S0urceror/MSX-USB/test/usb_via_arduino/src/main.parallel.cpp

// USB-HID - application that discovers attached USB devices to CH376s
// Copyright 2019 - Sourceror (Mario Smit)

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
#include <stdio.h>
#include <fcntl.h>
#include <termios.h>
#include <strings.h>
#include <string.h>
#include <unistd.h>
#include <stdlib.h>
#include <vector>
#include <string>
#include <locale>
#include <codecvt>
#include <thread>
#include <chrono>
#include <ctime>
#include <iostream>
#include <stdio.h>
#include <iomanip>

#define BOOT_PROTOCOL 0
#define HID_CLASS 0x03
#define HID_BOOT 0x01
#define HID_KEYBOARD 0x01
#define HID_MOUSE 0x02

//#define   B115200 0010002
//#define   B230400 0010003
#define   B460800 0010004
#define   B500000 0010005
#define   B576000 0010006
#define   B921600 0010007
#define  B1000000 0010010
#define  B1152000 0010011
#define  B1500000 0010012
#define  B2000000 0010013
#define  B2500000 0010014
#define  B3000000 0010015
#define  B3500000 0010016
#define  B4000000 0010017
#define BAUDRATE B115200
int serial=-1;

#define CH376_CMD_GET_IC_VER 0x01
#define CH375_CMD_SET_USB_SPEED 0x04
#define CH375_CMD_RESET_ALL 0x05
#define CH375_CMD_CHECK_EXIST 0x06
#define CH375_CMD_SET_USB_MODE 0x15
#define CH375_CMD_TEST_CONNECT 0x16
#define CH375_CMD_GET_STATUS 0x22
#define CH375_CMD_SET_USB_ADDR 0x13
#define CH375_CMD_SET_ENDP6 0x1C
#define CH375_CMD_SET_ENDP7 0x1D
#define CH375_CMD_RD_USB_DATA 0x27
#define CH375_CMD_RD_USB_DATA_UNLOCK     0x28
//#define CH375_CMD_WR_USB_DATA7 0x2B
#define CH375_CMD_WR_HOST_DATA 0x2C
#define CH376_CMD_SET_FILE_NAME 0x2F
#define CH376_CMD_DISK_CONNECT 0x30
#define CH376_CMD_DISK_MOUNT 0x31
#define CH376_CMD_OPEN_FILE 0x32
#define CH376_CMD_FILE_ENUM_GO 0x33
#define CH376_CMD_FILE_CLOSE 0x36
#define CH376_CMD_DIR_INFO_READ 0x37

#define CH376_CMD_BYTE_READ 0x3a
#define CH376_CMD_BYTE_RD_GO 0x3b
#define CH375_USB_INT_DISK_READ 0x1d

#define CH376_CMD_CLR_STALL 0x41
#define CH375_CMD_SET_ADDRESS 0x45
#define CH375_CMD_GET_DESCR 0x46
#define CH375_CMD_SET_CONFIG 0x49
#define CH375_CMD_ISSUE_TOKEN 0x4F
#define CH375_CMD_ISSUE_TKN_X 0x4E
#define CH375_CMD_ABORT_NAK 0x17
#define CH376_CMD_GET_REGISTER 0x0A
#define CH376_CMD_SET_REGISTER 0x0B

#define CH375_USB_MODE_HOST_NON_SOF 0x05
#define CH375_USB_MODE_HOST 0x06
#define CH375_USB_MODE_HOST_RESET 0x07

#define CH375_USB_ERR_OPEN_DIR 0x41
#define CH375_USB_ERR_MISS_FILE 0x42
#define CH375_USB_ERR_FOUND_NAME 0x43

#define CH375_USB_INT_SUCCESS 0x14
#define CH375_USB_INT_CONNECT 0x15
#define CH375_USB_INT_DISCONNECT 0x16
#define CH375_USB_INT_BUF_OVER 0x17
#define CH375_USB_INT_USB_READY 0x18

#define CH375_CMD_RET_SUCCESS 0x51
#define CH375_CMD_RET_ABORT 0x52

#define CH375_USB_DEVICE_DESCRIPTOR 0x01
#define CH375_USB_CONFIGURATION_DESCRIPTOR 0x02
#define CH375_USB_INTERFACE_DESCRIPTOR 0x04
#define CH375_USB_ENDPOINT_DESCRIPTOR 0x05

//--- PIDs
#define CH_PID_SETUP 0x0D
#define CH_PID_IN  0x09
#define CH_PID_OUT 0x01

uint8_t device_counter=1;
uint8_t max_packet_size;
#ifdef _VERBOSE_DEBUG
std::chrono::system_clock::time_point curtime;
#endif

typedef struct __attribute__((packed)) _USB_DEVICE_DESCRIPTOR {
     uint8_t bLength;
     uint8_t bDescriptorType;
     uint16_t bcdUSB;
     uint8_t bDeviceClass;
     uint8_t bDeviceSubClass;
     uint8_t bDeviceProtocol;
     uint8_t bMaxPacketSize0;
     uint16_t idVendor;
     uint16_t idProduct;
     uint16_t bcdDevice;
     uint8_t iManufacturer;
     uint8_t iProduct;
     uint8_t iSerial;
     uint8_t bNumConfigurations;
} USB_DEVICE_DESCRIPTOR;
USB_DEVICE_DESCRIPTOR device;

 typedef struct __attribute__((packed)) _USB_CONFIG_DESCRIPTOR {
     uint8_t bLength;
     uint8_t bDescriptorType;
     uint16_t wTotalLength;
     uint8_t bNumInterfaces;
     uint8_t bConfigurationvalue;
     uint8_t iConfiguration;
     uint8_t bmAttributes;
     uint8_t bMaxPower;
 } USB_CONFIG_DESCRIPTOR;

typedef struct __attribute__((packed)) _USB_HID_DESCRIPTOR {
    uint8_t bLength;
    uint8_t bDescriptorType;
    uint16_t hid_version;
    uint8_t country_code;
    uint8_t num_descriptors;
    uint8_t descriptor_type;
    uint16_t descriptor_length;
} USB_HID_DESCRIPTOR;

 typedef struct __attribute__((packed)) _USB_INTERF_DESCRIPTOR {
     uint8_t bLength;
     uint8_t bDescriptorType;
     uint8_t bInterfaceNumber;
     uint8_t bAlternateSetting;
     uint8_t bNumEndpoints;
     uint8_t bInterfaceClass;
     uint8_t bInterfaceSubClass;
     uint8_t bInterfaceProtocol;
     uint8_t iInterface;
 } USB_INTERF_DESCRIPTOR;

 typedef struct __attribute__((packed)) _USB_ENDPOINT_DESCRIPTOR {
     uint8_t bLength;
     uint8_t bDescriptorType;
     uint8_t bEndpointAddress;
     uint8_t bmAttributes;
     uint16_t wMaxPacketSize;
     uint8_t bInterval;
 } USB_ENDPOINT_DESCRIPTOR;

typedef struct __attribute__((packed)) _USB_ETHERNET_DESCRIPTOR {
     uint8_t bLength;
     uint8_t bDescriptorType;
     uint8_t bDescriptorSubType;
     uint8_t iMACAddress;
     uint32_t bmEthernetStatistics;
     uint16_t wMaxSegmentSize;
     uint16_t wNumberMCFilters;
     uint8_t bNumberPowerFilters;
 } USB_ETHERNET_DESCRIPTOR;

typedef struct __attribute__((packed)) _USB_ETHERNET_HEADER_DESCRIPTOR {
     uint8_t bLength;
     uint8_t bDescriptorType;
     uint8_t bDescriptorSubType;
     uint16_t bcdCDC;
 } USB_ETHERNET_HEADER_DESCRIPTOR;

typedef struct __attribute__((packed)) _USB_ETHERNET_UNION_DESCRIPTOR {
     uint8_t bLength;
     uint8_t bDescriptorType;
     uint8_t bDescriptorSubType;
     uint8_t bControlInterface;
     uint8_t bSubordinateInterface0;
     uint8_t bSubordinateInterface1;
     uint8_t bSubordinateInterface2;
     uint8_t bSubordinateInterface3;
 } USB_ETHERNET_UNION_DESCRIPTOR;

typedef struct __attribute__((packed)) _USB_HUB_DESCRIPTOR 
{
     uint8_t bLength;
     uint8_t bDescriptorType;
     uint8_t bNrPorts;
     uint16_t wHubCharacteristics;
     uint8_t bPwrOn2PwrGood;
     uint8_t bHubContrCurrent;
     uint8_t DeviceRemovable;
     uint8_t PortPwrCtrlMask;
} USB_HUB_DESCRIPTOR;

struct _hid_info 
{
    uint8_t mouse_endpoint,mouse_millis,mouse_interface=255;
    uint16_t mouse_packetsize;
    uint8_t keyboard_endpoint,keyboard_millis,keyboard_interface=255;
    uint16_t keyboard_packetsize;
    uint8_t configuration_id=0;
    uint8_t device_address;
}* hid_info=NULL;
struct _ethernet_info 
{
    uint8_t ethernet_data_interface=255,ethernet_control_interface=255;
    uint8_t ethernet_interrupt_endpoint,ethernet_bulk_in_endpoint,ethernet_bulk_out_endpoint;
    uint8_t ethernet_interrupt_millis;
    uint16_t ethernet_interrupt_packetsize,ethernet_bulk_in_packetsize,ethernet_bulk_out_packetsize;
    uint8_t configuration_id=0;
    uint8_t ethernet_alternate_setting;
    uint8_t device_address;
}* ethernet_info=NULL;
struct _hub_info
{
    uint8_t hub_interface=255;
    uint8_t configuration_id=0;
    uint8_t hub_interrupt_endpoint;
    uint16_t hub_interrupt_packetsize;
    uint8_t hub_interrupt_millis;
    uint8_t device_address;
}* hub_info=NULL;
struct _storage_info
{
    uint8_t interface_id=255;
    uint8_t configuration_id=0;
    uint8_t bulk_in_endpoint_id=0;
    uint8_t bulk_in_packetsize;
    uint8_t bulk_in_toggle=0;
    uint8_t bulk_out_endpoint_id=0;
    uint8_t bulk_out_packetsize;
    uint8_t bulk_out_toggle=0;
    uint8_t device_address;
    uint32_t tag = 1;
}* storage_info=NULL;
typedef struct __attribute__((packed)) _command_block_wrapper 
{
    uint32_t dCBWSignature = 0x43425355;
    uint32_t dCBWTag = 1;
    uint32_t dCBWDataTransferLength;
    uint8_t bmCBWFlags;
    uint8_t bCBWLUN;
    uint8_t bCBWCBLength;
    uint8_t data [16];
} command_block_wrapper;
typedef struct __attribute__((packed)) _command_status_wrapper 
{
    uint32_t dCBWSignature;
    uint32_t dCBWTag;
    uint32_t dCSWDataResidue;
    uint8_t bCSWStatus;
} command_status_wrapper;
typedef struct __attribute__((packed)) _scsi_inquiry
{
    uint8_t bOperationCode = 0x12;
    uint8_t bLUN=0;
    uint8_t bReserved1=0;
    uint8_t bReserved2=0;
    uint8_t bAllocationLength = 0x24;
    uint8_t bReserved3=0;
    //uint8_t pad [6] = {0,0,0,0,0,0};
} scsi_inquiry;
typedef struct __attribute__((packed)) _scsi_read10
{
    uint8_t bOperationCode = 0x28;
    uint8_t bLUN=0;
    uint32_t dLBA=0;
    uint8_t bReserved1=0;
    uint16_t wTransferLength=0;
    uint8_t bReserved2=0;
    //uint8_t pad [2]={0,0};
} scsi_read10;
typedef struct __attribute__((packed)) _scsi_request_sense
{
    uint8_t bOperationCode = 0x03;
    uint8_t bLUN=0;
    uint8_t bReserved1=0;
    uint8_t bReserved2=0;
    uint8_t bAllocationLength = 18;
    uint8_t bReserved3=0;
    //uint8_t pad [6] = {0,0,0,0,0,0};
} scsi_request_sense;
typedef struct __attribute__((packed)) _scsi_test_unit_ready
{
    uint8_t bOperationCode = 0x00;
    uint8_t bLUN=0;
    uint8_t bReserved1=0;
    uint8_t bReserved2=0;
    uint8_t bReserved3=0;
    uint8_t bReserved4=0;
    //uint8_t pad [6] = {0,0,0,0,0,0};
} scsi_test_unit_ready;
typedef struct __attribute__((packed)) _scsi_mode_sense6
{
    uint8_t bOperationCode = 0x1a;
    uint8_t bLUN=0;
    uint8_t bPageCode=0;
    uint8_t bSubpageCode=0;
    uint8_t bAllocationLength=0;
} scsi_mode_sense6;
typedef struct __attribute__((packed)) _scsi_capacity
{
    uint8_t bOperationCode = 0x25;
    uint8_t bLUN=0;
    uint8_t pad[8] = {0,0,0,0,0,0,0,0};
} scsi_capacity;

bool VERBOSE=1;
void print_buffer (uint8_t* data, uint16_t length)
{
    if (VERBOSE==0)
        return;

    for (int i=0;i<length;i++)
    {
        if ((i%16)==0)
            printf ("\n");
        if ((i%4)==0)
            printf (" ");
        printf ("%02x ",*(data+i));
    }
    printf ("\n");
}

void error (char const * msg)
{
    printf ("ERROR: %s\n",msg);
    exit(0);
}

void init_serial (const char* device)
{
    serial = open(device, O_RDWR | O_NOCTTY | O_NONBLOCK);
    if(serial == -1)
      error( "failed to open port" );
    if(!isatty(serial))
      error( "not serial" );
    fcntl(serial, F_SETFL, 0);
    
    struct termios  config;
    bzero(&config, sizeof(config));
    config.c_cflag |= CS8 | CLOCAL | CREAD;
    config.c_iflag |= IGNPAR;
    cfsetispeed (&config, B230400);
    cfsetospeed (&config, B230400);
     
    config.c_cc[VTIME]    = 1;   /* wait 0.1 * VTIME on new characters to arrive when blocking */
    config.c_cc[VMIN]     = 1;   /* blocking read until 1 chars received */
    
    tcflush(serial, TCIFLUSH);
    tcsetattr(serial, TCSANOW, &config); 
}

// LOW_LEVEL serial communication to CH376
///////////////////////////////////////////////////////////////////////////
const uint8_t WR_COMMAND = 1;
const uint8_t RD_STATUS = 2;
const uint8_t WR_DATA = 3;
const uint8_t RD_DATA = 4;
const uint8_t RD_INT = 5;
const uint8_t RD_DATA_MULTIPLE = 6;
const uint8_t WR_DATA_MULTIPLE = 7;
const uint8_t DATA_DUMP = 10;
const uint8_t SPI_WRITE_MULTIPLE = 11;

void testspeed ()
{
    uint8_t new_value;
    uint8_t cmd = DATA_DUMP;
    int i;
    write (serial, &cmd, 1);

    auto t1 = std::chrono::high_resolution_clock::now();
    for (i=0;i<10*512;i++) {
        int bytes = read (serial,&new_value,1);
        if (bytes!=1)
            error ("Serial max speed test did not receive all expected bytes");
        if (new_value!=0xaa)
            error ("Wrong data returned");
    }
    auto t2 = std::chrono::high_resolution_clock::now();
    auto duration = std::chrono::duration_cast<std::chrono::microseconds>( t2 - t1 ).count();
    std::cout << "Serial max read speed: " << i / (duration/1000000.0) << " bytes/second" << std::endl;
}
#ifdef _VERBOSE_DEBUG
std::string getCommandName(uint8_t command)
{
  std::string cmdstr;
  switch (command)
  {
    case 0x01:  cmdstr = "CH_CMD_GET_IC_VER";
                break;
    case 0x04:  cmdstr = "CH_CMD_SET_SPEED";
                break;
    case 0x05:  cmdstr = "CH_CMD_RESET_ALL";
                break;
    case 0x06:  cmdstr = "CH_CMD_CHECK_EXIST";
                break;
    case 0x0b:  cmdstr = "CH_CMD_SET_REGISTER"; // SET_RETRY, SD0_INT
                break;
    case 0x0f:  cmdstr = "CH_CMD_DELAY_100US";
                break;
    case 0x13:  cmdstr = "CH_CMD_SET_USB_ADDR";
                break;
    case 0x15:  cmdstr = "CH_CMD_SET_USB_MODE";
                break;
    case 0x16:  cmdstr = "CH_CMD_TEST_CONNECT";
                break;
    //case 0x17:  cmdstr = "CH_CMD_ABORT_NAK";
    //            break;
    case 0x22:  cmdstr = "CH_CMD_GET_STATUS";
                break;
    case 0x27:  cmdstr = "CH_CMD_RD_USB_DATA0";
                break;
    case 0x2c:  cmdstr = "CH_CMD_WR_HOST_DATA";
                break;
    case 0x4e:  cmdstr = "CH_CMD_ISSUE_TKN_X";
                break;
    case 0x46:  cmdstr = "CH_CMD_GET_DESCR";
                break;
    case 0x41:  cmdstr = "CH_CMD_CLR_STALL";
                break;
    case 0x30:  cmdstr = "CH_CMD_DISK_CONNECT";
                break;
    case 0x31:  cmdstr = "CH_CMD_DISK_MOUNT";
                break;
    case 0x32:  cmdstr = "CH_CMD_FILE_OPEN";
                break;
    case 0x36:  cmdstr = "CH_CMD_FILE_CLOSE";
                break;                
    case 0x33:  cmdstr = "CH_CMD_FILE_ENUM_GO";
                break;                                
    case 0x2f:  cmdstr = "CH_CMD_SET_FILE_NAME";
                break;
    case 0x3a:  cmdstr = "CH_CMD_BYTE_READ";
                break;
    case 0x3b:  cmdstr = "CH_CMD_BYTE_RD_GO";
                break;        
    case 0x3c:  cmdstr = "CH_CMD_BYTE_WRITE";
                break;
    case 0x3d:  cmdstr = "CH_CMD_BYTE_WR_GO";
                break;         
    case 0x40:  cmdstr = "CH_CMD_DIR_CREATE";
                break;   
    case 0x34:  cmdstr = "CH_CMD_FILE_CREATE";
                break;    
    case 0x2d:  cmdstr = "CH_CMD_WR_REQ_DATA";
                break;      
    case 0x37:  cmdstr = "CH_CMD_DIR_INFO_READ";
                break;       
    case 0x39:  cmdstr = "CH_CMD_BYTE_LOCATE";
                break;           
    case 0x35:  cmdstr = "CH_CMD_FILE_ERASE";
                break;        
    default:cmdstr = "UNKNOWN";
            break;
  }
  return cmdstr;
}
#endif
void writeCommand (uint8_t command)
{
    #ifdef _VERBOSE_DEBUG
    std::chrono::system_clock::time_point prevtime = curtime;
    curtime = std::chrono::system_clock::now();
    time_t time = std::chrono::system_clock::to_time_t(curtime);
    std::clog << std::put_time (std::localtime(&time),"%T") << ":" << std::setw(4) << std::setfill('0') << (std::chrono::duration_cast<std::chrono::milliseconds>(curtime - prevtime).count()) << " ";
    std::clog << "writeCommand (" << getCommandName (command) << ") 0x" << std::hex << std::setw(2) << std::setfill('0') << unsigned (command) << std::dec << std::endl;
    #endif

    uint8_t cmd[] = {WR_COMMAND,command};
    write (serial,cmd,sizeof(cmd));
}
void writeData (uint8_t data)
{
    #ifdef _VERBOSE_DEBUG
    std::clog << "writeData (0x" << std::hex << std::setw(2) << std::setfill('0') << unsigned (data) << ")" << std::dec << std::endl;
    #endif
    uint8_t cmd[] = {WR_DATA,data};
    write (serial,cmd,sizeof(cmd));
}
void writeDataMultiple (uint8_t* buffer,uint8_t len)
{
    uint8_t cmd[] = {WR_DATA_MULTIPLE,len};
    write (serial,cmd,sizeof(cmd));
    write (serial,buffer,len);
    #ifdef _VERBOSE_DEBUG
    std::clog << "writeDataMultiple: ";
    for (int i=0;i<len;i++) {
      std::clog << (i==0?"":",") << "0x" << std::hex << std::setw(2) << std::setfill('0') << unsigned (buffer[i]) << std::dec ;
    }
    std::clog << std::endl;
    #endif
}
ssize_t readData (uint8_t* new_value)
{
    uint8_t cmd[] = {RD_DATA};
    write (serial,cmd,sizeof(cmd));
    ssize_t bytes = read (serial,new_value,1);
    #ifdef _VERBOSE_DEBUG
    std::clog << "0x" << std::hex << std::setw(2) << std::setfill('0') << unsigned (*new_value) << std::dec << " = readData ()" << std::endl;
    #endif
    return bytes;
}
ssize_t readDataMultiple (uint8_t* buffer,uint8_t len)
{
    int i;
    uint8_t *pTemp = buffer;

    uint8_t cmd[] = {RD_DATA_MULTIPLE,len};
    write (serial,cmd,sizeof(cmd));
    uint8_t bytes_read = 0;
    while (bytes_read<len)
    {
        uint8_t bytes = read (serial,buffer,len);
        if (bytes==0) 
            error ("did not receive data");
        bytes_read += bytes;
        buffer += bytes;
    }
    assert (bytes_read==len);
    #ifdef _VERBOSE_DEBUG
    std::clog << "readDataMultiple: ";
    for (int i=0;i<bytes_read;i++) {
      std::clog << (i==0?"":",") << "0x" << std::hex << std::setw(2) << std::setfill('0') << unsigned (pTemp[i]) << std::dec ;
    }
    std::clog << std::endl;
    #endif
    return bytes_read;
}
ssize_t readStatus (uint8_t* new_value)
{
    uint8_t cmd[] = {RD_STATUS};
    write (serial,cmd,sizeof(cmd));
    return read (serial,new_value,1);
}
ssize_t readInterrupt (uint8_t* new_value)
{
    uint8_t cmd[] = {RD_INT};
    write (serial,cmd,sizeof(cmd));
    return read (serial,new_value,1);
}

// CHECK STATUS
///////////////////////////////////////////////////////////////////////////
uint8_t waitInterrupt ()
{
    uint8_t status,interrupt;
    int i=0;
    ssize_t bytes;
    int counter = 1000;
    while ((bytes=readInterrupt(&interrupt)) && counter>0)
    {
        if (interrupt&0x80)
            break;
        usleep (1000);
        counter --;
    }
    if (counter<=0)
        error ("timeout waitInterrupt");
    writeCommand(CH375_CMD_GET_STATUS);
    bytes = readData (&status);
    if (bytes)
        return status;
    return 0;
}
uint8_t waitStatus ()
{
    uint8_t status,interrupt;
    int i=0;
    ssize_t bytes;
    int counter = 500;
    while ((bytes=readStatus(&interrupt)) && counter>0)
    {
        if ((interrupt&0x80)==0)
            break;
        usleep (1000);
        counter --;
    }
    if (counter<=0)
    {
        printf ("timeout waitStatus\n");
        return 0;
    }
    writeCommand(CH375_CMD_GET_STATUS);
    bytes = readData (&status);
    if (bytes)
        return status;
    return 0;
}
void check_exists ()
{
    uint8_t value = 190;
    uint8_t new_value=0;
    //char cmd[] = {0x57,0xAB,CH375_CMD_CHECK_EXIST,value};
    writeCommand (CH375_CMD_CHECK_EXIST);
    writeData(value);
    ssize_t bytes = readData (&new_value);
    value = value ^ 255;
    if (bytes!=1 || (new_value != value))
        error ("Device does not exist\n");
}

// CH376 built-in commands
///////////////////////////////////////////////////////////////////////////
void reset_all ()
{
    writeCommand (CH375_CMD_RESET_ALL);
    usleep (100000);
}
void set_target_device_address (uint8_t address)
{
    writeCommand (CH375_CMD_SET_USB_ADDR);
    writeData(address);
    usleep (2000);
}

bool set_usb_host_mode (uint8_t mode)
{
    writeCommand(CH375_CMD_SET_USB_MODE);
    writeData(mode);
    
    uint8_t value;
    for(int i=0; i!=200; i++ )
    {
        readData(&value);
        if ( value == CH375_CMD_RET_SUCCESS )
            return true;
        usleep(1000);
    }
    return false;
}

#define VAR_SYS_BASE_INFO 0x20
#define VAR_RETRY_TIMES 0x25
#define VAR_FILE_BIT_FLAG 0x26
#define VAR_DISK_STATUS 0x2b
#define VAR_SD_BIT_FLAG 0x30
#define VAR_UDISK_TOGGLE 0x31
#define VAR_UDISK_LUN 0x34
#define VAR_SEC_PER_CLUS 0x38
#define VAR_FILE_DIR_INDEX 0x3b
#define VAR_CLUS_SEC_OFS 0x3c
#define VAR_DISK_ROOT 0x44
#define VAR_DSK_TOTAL_CLUS 0x48
#define VAR_DSK_START_LBA 0x4c
#define VAR_DSK_DAT_START 0x50
#define VAR_LBA_BUFFER 0x54
#define VAR_LBA_CURRENT 0x58
#define VAR_FAT_DIR_LBA 0x5c
#define VAR_START_CLUSTER 0x60
#define VAR_CURRENT_CLUST 0x64
#define VAR_FILE_SIZE 0x68
#define VAR_CURRENT_OFFSET 0x6c

void set_register (uint8_t reg, uint8_t value)
{
    writeCommand (CH376_CMD_SET_REGISTER);
    writeData (reg); 
    writeData (value);
}
uint8_t get_register (uint8_t reg)
{
    writeCommand (CH376_CMD_GET_REGISTER);
    writeData (reg); 
    uint8_t value=0;
    readData (&value);
    return value;
}


//Bits 7 and 6:
//  0x: Don't retry NAKs
//  10: Retry NAKs indefinitely (default)
//  11: Retry NAKs for 3s
//Bits 5-0: Number of retries after device timeout
//Default after reset and SET_USB_MODE is 8Fh
void set_retry (uint8_t mode)
{
    set_register (VAR_RETRY_TIMES,mode);
}

void set_speed (uint8_t speed)
{
    writeCommand (CH375_CMD_SET_USB_SPEED);
    writeData(speed);
}
void set_address (uint8_t address)
{
     writeCommand (CH375_CMD_SET_ADDRESS);
     writeData(address);
     if (waitStatus ()!=CH375_USB_INT_SUCCESS)
         error ("ERROR: address not set\n");
}
void set_configuration (uint8_t configuration)
{
     writeCommand(CH375_CMD_SET_CONFIG);
     writeData(configuration);
     if (waitStatus ()!=CH375_USB_INT_SUCCESS)
         error ("ERROR: configuration not set\n");
}
bool get_device_descriptor ()
{
    uint8_t value;
    ssize_t bytes;
    
    writeCommand(CH375_CMD_GET_DESCR);
    writeData(CH375_USB_DEVICE_DESCRIPTOR);
    if (waitStatus ()!=CH375_USB_INT_SUCCESS)
        error ("ERROR: USB device descriptor not read 1\n");
    writeCommand(CH375_CMD_RD_USB_DATA);
    // read length of return package
    value = 0;
    bytes = readData(&value);
    if (bytes==1 && value == sizeof (USB_DEVICE_DESCRIPTOR))
    {
        bytes = readDataMultiple ((uint8_t*)&device,sizeof (USB_DEVICE_DESCRIPTOR));
        if (bytes!=value)
            error ("ERROR: USB device descriptor not read 2\n");
    }
    else
        error ("ERROR: USB device descriptor not read 3\n");
    return true;
}

// Higher level USB read/write
///////////////////////////////////////////////////////////////////////////
void write_usb_data (uint8_t* message,uint8_t length)
{
    writeCommand (CH375_CMD_WR_HOST_DATA);
    writeData(length);
    writeDataMultiple (message,length);
    //writeData(length);
    //for (int i=0;i<length;i++)
    //    writeData(message[i]);
}
void issue_token (uint8_t endpoint_number, uint8_t pid, uint8_t in_toggle, uint8_t out_toggle)
{
    writeCommand(CH375_CMD_ISSUE_TKN_X);
    writeData(in_toggle<<7 | out_toggle<<6);
    writeData(endpoint_number << 4 | pid);
}

ssize_t read_usb_data (uint8_t* pBuffer,uint16_t maxlen)
{
    uint8_t value = 0;
    writeCommand(CH375_CMD_RD_USB_DATA);
    ssize_t bytes = readData(&value);
    if (bytes==0)
        error ("no data available");
    if (value==0)
        return 0;
    if (value>maxlen)
        value=maxlen;
    bytes = readDataMultiple(pBuffer, value);
    if (bytes<value)
        error("did not receive enough bytes");
    return bytes;
}

// USB data packet input
///////////////////////////////////////////////////////////////////////////
uint8_t data_in_transfer (uint16_t length, uint8_t target_device_address, uint8_t endpoint_number, uint8_t endpoint_packetsize, uint8_t& endpoint_toggle,uint8_t* result)
{
    uint16_t remaining_data_length = length;
    bzero(result, length);
    uint8_t* pTemp = result;
    uint8_t status;
    int bytes_read=0;
    
    set_target_device_address(target_device_address);
    
    while (remaining_data_length>0)
    {
        issue_token(endpoint_number, CH_PID_IN, endpoint_toggle, 0);
        if ((status=waitStatus())!=CH375_USB_INT_SUCCESS)
            return status;
        endpoint_toggle = endpoint_toggle ^ 1;
        bytes_read = read_usb_data (pTemp,length);
        remaining_data_length -= bytes_read;
        pTemp += bytes_read;
        
        if (bytes_read<endpoint_packetsize)
            break;
    }
    return CH375_USB_INT_SUCCESS;// length-remaining_data_length;
}

// USB data packet output
///////////////////////////////////////////////////////////////////////////
uint8_t data_out_transfer (uint8_t* pBuffer,uint16_t length, uint8_t target_device_address, uint8_t endpoint_number, uint8_t endpoint_packetsize, uint8_t& endpoint_toggle)
{
    uint8_t* pTemp = pBuffer;
    uint16_t remaining_data_length = length;
    uint8_t status;

    set_target_device_address(target_device_address);
    
    while (remaining_data_length>0)
    {
        int amountwritten=endpoint_packetsize<remaining_data_length?endpoint_packetsize:remaining_data_length;
        write_usb_data(pTemp, amountwritten);
        issue_token(endpoint_number, CH_PID_OUT, 0, endpoint_toggle);
        if ((status=waitStatus())!=CH375_USB_INT_SUCCESS)
        {
            return status;
            /*
            //error ("unable to output data in time");
            if ((status&0x2f)==0b00101010) // 2A
            {
                printf (">> NAK <<\n");
                return;
            }
            if ((status&0x2f)==0b00101110) // 2E
            {
                printf (">> STALL <<\n");
                // un-stall endpoint
                writeCommand (CH376_CMD_CLR_STALL);
                writeData (endpoint_number);
                waitStatus ();
                continue;
            }
            if ((status&0x23)==0b00100000) // 20
            {
                printf (">> OVER TIME <<\n");
                return;
            }
            printf (">> UNEXPECTED 0x%x <<\n",status);
            */
        }
        pTemp+=amountwritten;
        remaining_data_length-=amountwritten;
        endpoint_toggle = endpoint_toggle ^ 1;
    }
    return CH375_USB_INT_SUCCESS;
}

#define IN 1
#define OUT 0
// USB command execution via SETUP, DATA, STATUS stages
///////////////////////////////////////////////////////////////////////////
bool execute_control_transfer (uint8_t target_device_address,uint8_t message[8],uint8_t* data,uint8_t data_len)
{
    uint8_t status;
    uint16_t requested_length = (*(message + 6))+((*(message +7))<<8);
    uint8_t data_direction = message[0]&0b10000000?IN:OUT;

    //print_buffer (message,8);
    set_target_device_address(target_device_address);
    
    //Setup stage
    write_usb_data (message,8);
    uint8_t endpoint = 0;
    issue_token (endpoint, CH_PID_SETUP,0,0);
    uint8_t interrupt = waitStatus();
    if (interrupt != CH375_USB_INT_SUCCESS)
        return false;
    
    //Data stage
    uint8_t endpoint_toggle = 1;
    if (data_direction==IN)
    {
        status = data_in_transfer(requested_length, target_device_address, 0, max_packet_size, endpoint_toggle,data);
        if (status != CH375_USB_INT_SUCCESS)
        {
            if ((status&0x2f)==0b00101110)
            {
                printf (">> STALL 1 <<\n");
                // un-stall endpoint
                writeCommand (CH376_CMD_CLR_STALL);
                writeData (0x80+endpoint);

                status=waitStatus();
                //if (status!=CH375_USB_INT_SUCCESS)
                //    return false;

                usleep (250000);
                return execute_control_transfer (target_device_address,message,data,data_len);
            }
            return false;
        }
    }
    else
    {
        status = data_out_transfer (data,requested_length, target_device_address, 0, max_packet_size, endpoint_toggle);
        if (status!=CH375_USB_INT_SUCCESS)
        {
            if ((status&0x2f)==0b00101010) // 2A
            {
                printf (">> NAK <<\n");
                return false;
            }
            if ((status&0x2f)==0b00101110) // 2E
            {
                printf (">> STALL 2 <<\n");
                // un-stall endpoint
                writeCommand (CH376_CMD_CLR_STALL);
                writeData (endpoint);
                status=waitStatus();
                if (status!=CH375_USB_INT_SUCCESS)
                    return false;

                usleep (250000);
                return execute_control_transfer (target_device_address,message,data,data_len);
            }
            if ((status&0x23)==0b00100000) // 20
            {
                printf (">> OVER TIME <<\n");
                return false;
            }
            printf (">> UNEXPECTED 0x%x <<\n",status);
            return false;
        }
    }
    
    // Status stage
    if (data_direction==OUT || requested_length==0)
    {
        issue_token(endpoint, CH_PID_IN, 1, 0);
        while ((waitStatus()&0x2f)==0x2a); // absorb NAK
        uint8_t tmp[64]; 
        read_usb_data ((uint8_t*)&tmp,64);
    }
    else
    {
        issue_token(endpoint, CH_PID_OUT, 0, 1);
        interrupt = waitStatus();
        /*
        uint8_t interrupt;
        while (true)
        {
            interrupt = waitStatus();
            if ((interrupt&0x2f)==0x2a) // absorb NAK
                return false;
            if ((interrupt&0x2f)==0x2e) // absorb STALL
            {
                printf (">> STALL 3 <<\n");
                // un-stall endpoint
                writeCommand (CH376_CMD_CLR_STALL);
                writeData (0x80+endpoint);
                if (waitStatus ()!=CH375_USB_INT_SUCCESS)
                    return false;

                usleep (250000);
                return execute_control_transfer (target_device_address,message,data,data_len);
            }
            break;
        };
        if (interrupt!=CH375_USB_INT_SUCCESS)
            return false;
        */
    }
    return true;
}

// DESCRIPTOR commands
///////////////////////////////////////////////////////////////////////////
bool get_device_descriptor2 (uint8_t target_device_address,uint8_t* buffer, int& buffer_length)
{
    uint8_t cmd[] = {0x80,6,0,1,0,0,sizeof (USB_DEVICE_DESCRIPTOR),0};
    max_packet_size = 8;
    uint8_t* data=(uint8_t*) malloc (sizeof (USB_DEVICE_DESCRIPTOR));
    
    //bool result = execute_control_transfer(target_device_address,cmd,NULL,max_packet_size,0,data);
    bool result = execute_control_transfer(target_device_address,cmd,data,sizeof (USB_DEVICE_DESCRIPTOR));
    if (result)
    {
        print_buffer (data,*(data));
        memcpy(buffer, data, *(data));
        memcpy(&device, data, *(data));
        buffer_length=*(data);
        max_packet_size = device.bMaxPacketSize0;
    }
    free(data);
    return result;
}
bool get_configuration_descriptor2 (uint8_t target_device_address,uint8_t config_id,uint8_t* buffer,int &buffer_length)
{
    uint8_t cmd[] = {0x80,6,config_id,2,0,0,sizeof(USB_CONFIG_DESCRIPTOR),0};
    uint8_t* data=(uint8_t*) malloc (max_packet_size);
    bool result2 = false;
    //bool result = execute_control_transfer(target_device_address,cmd,NULL,max_packet_size,0,data);
    bool result = execute_control_transfer(target_device_address,cmd,data,max_packet_size);
    if (result)
    {
        USB_CONFIG_DESCRIPTOR* config = (USB_CONFIG_DESCRIPTOR*) data;
        uint8_t cmd2[] = {0x80,6,config_id,2,0,0,(uint8_t)config->wTotalLength,0};
        uint8_t* data2=(uint8_t*) malloc (config->wTotalLength);
        //result2 = execute_control_transfer(target_device_address,cmd2,NULL,max_packet_size,0,data2);
        result2 = execute_control_transfer(target_device_address,cmd2,data2,config->wTotalLength);
        if (result2)
        {
            memcpy (buffer, data2,config->wTotalLength);
            buffer_length += config->wTotalLength;
            print_buffer (data2,config->wTotalLength);
        }
        free (data2);
    }
    free (data);
    return result && result2;
}

std::string utf16_to_utf8(std::u16string const& s)
{
    std::wstring_convert<std::codecvt_utf8_utf16<char16_t, 0x10ffff>, char16_t> cnv;
    std::string utf8 = cnv.to_bytes(s);
    if(cnv.converted() < s.size())
        throw std::runtime_error("incomplete conversion");
    return utf8;
}

const char no_data[] = "{no data}";
std::string get_string2 (uint8_t target_device_address,uint8_t string_id)
{
    if (string_id==0)
        return no_data;
    
    uint8_t cmd[] = {0x80,6,string_id,3,0,0,max_packet_size,0};
    uint8_t* data=(uint8_t*) malloc (max_packet_size);
    std::string str8;
    //bool result = execute_control_transfer(target_device_address,cmd,NULL,max_packet_size,0,data);
    bool result = execute_control_transfer(target_device_address,cmd,data,max_packet_size);
    if (result)
    {
        uint8_t len = data[0];
        uint8_t type = data[1];
        std::u16string str = (char16_t*) (data+2);
        str8 = utf16_to_utf8(str);
    }
    free (data);
    return str8;
}

// USB HID COMMANDS
///////////////////////////////////////////////////////////////////////////
bool set_report2 (uint8_t target_device_address,uint8_t report_type,uint8_t report_id,uint8_t interface,uint8_t* report,uint8_t report_size)
{
    uint8_t cmd[] = {0x21,0x09,report_id,report_type,interface,0,report_size,0};
    bool result = execute_control_transfer(target_device_address,cmd,report,report_size);
    return result;
}
bool set_protocol2 (uint8_t target_device_address,uint8_t protocol_id,uint8_t interface)
{
    uint8_t cmd[] = {0x21,0x0B,protocol_id,0,interface,0,0,0};
    uint8_t* data=(uint8_t*) malloc (max_packet_size);
    //bool result = execute_control_transfer(target_device_address,cmd,NULL,max_packet_size,0,data);
    bool result = execute_control_transfer(target_device_address,cmd,data,max_packet_size);
    free (data);
    return result;
}
bool set_idle2 (uint8_t target_device_address,uint8_t duration,uint8_t report_id, uint8_t interface)
{
    uint8_t cmd[] = {0x21,0x0A,report_id,duration,interface,0,0,0};
    uint8_t* data=(uint8_t*) malloc (max_packet_size);
    //bool result = execute_control_transfer(target_device_address,cmd,NULL,max_packet_size,0,data);
    bool result = execute_control_transfer(target_device_address,cmd,data,max_packet_size);
    free (data);
    return result;
}

// USB STORAGE COMMANDS
///////////////////////////////////////////////////////////////////////////
uint8_t get_max_luns (uint8_t target_device_address,uint8_t interface)
{
    uint8_t nr_luns = 0;
    uint8_t cmd[] = {0b10100001,0b11111110,0,0,interface,0,1,0};
    uint8_t* data=(uint8_t*) malloc (max_packet_size);
    //bool result = execute_control_transfer(target_device_address,cmd,NULL,max_packet_size,0,data);
    bool result = execute_control_transfer(target_device_address,cmd,data,max_packet_size);
    if (result)
        nr_luns = *data;
    free (data);
    return nr_luns;
}
bool bulkonly_mass_storage_reset (uint8_t target_device_address,uint8_t interface)
{
    uint8_t cmd[] = {0b00100001,0b11111111,0,0,interface,0,0,0};
    uint8_t* data=(uint8_t*) malloc (max_packet_size);
    //bool result = execute_control_transfer(target_device_address,cmd,NULL,max_packet_size,0,data);
    bool result = execute_control_transfer(target_device_address,cmd,data,max_packet_size);
    
    free (data);
    return result;
}

// USB COMMANDS
///////////////////////////////////////////////////////////////////////////
bool set_address2 (uint8_t target_device_address)
{
    uint8_t cmd[] = {0x00,0x05,target_device_address,0,0,0,0,0};
    uint8_t* data=(uint8_t*) malloc (max_packet_size);
    //bool result = execute_control_transfer(0,cmd,NULL,max_packet_size,0,data);
    bool result = execute_control_transfer(0,cmd,data,max_packet_size);
    free (data);
    return result;
}
bool set_configuration2 (uint8_t target_device_address,uint8_t configuration_id)
{
    uint8_t cmd[] = {0x00,0x09,configuration_id,0,0,0,0,0};
    uint8_t* data=(uint8_t*) malloc (max_packet_size);
    //bool result = execute_control_transfer(target_device_address,cmd,NULL,max_packet_size,0,data);
    bool result = execute_control_transfer(target_device_address,cmd,data,max_packet_size);
    free (data);
    return result;
}
bool set_interface2 (uint8_t target_device_address,uint8_t interface_id,uint8_t alternative_setting)
{
    uint8_t cmd[] = {0x01,11,alternative_setting,0,interface_id,0,0,0};
    uint8_t* data=(uint8_t*) malloc (max_packet_size);
    //bool result = execute_control_transfer(target_device_address,cmd,NULL,max_packet_size,0,data);
    bool result = execute_control_transfer(target_device_address,cmd,data,max_packet_size);
    free (data);
    return result;
}
bool clear_endpoint_feature2 (uint8_t target_device_address,uint8_t endpoint_id)
{
    uint8_t cmd[] = {0b00000010,1,0,0,endpoint_id,0,0,0};
    uint8_t* data=(uint8_t*) malloc (max_packet_size);
    //bool result = execute_control_transfer(target_device_address,cmd,NULL,max_packet_size,0,data);
    bool result = execute_control_transfer(target_device_address,cmd,data,max_packet_size);
    free (data);
    return result;
}
bool set_endpoint_feature2 (uint8_t target_device_address,uint8_t endpoint_id)
{
    uint8_t cmd[] = {0b00000010,3,0,0,endpoint_id,0,0,0};
    uint8_t* data=(uint8_t*) malloc (max_packet_size);
    //bool result = execute_control_transfer(target_device_address,cmd,NULL,max_packet_size,0,data);
    bool result = execute_control_transfer(target_device_address,cmd,data,max_packet_size);
    free (data);
    return result;
}
uint16_t get_endpoint_status (uint8_t target_device_address,uint8_t endpoint_id)
{
    uint16_t status = 0;
    uint8_t cmd[] = {0b10000010,0,0,0,endpoint_id,0,2,0};
    uint8_t* data=(uint8_t*) malloc (max_packet_size);
    //bool result = execute_control_transfer(target_device_address,cmd,NULL,max_packet_size,0,data);
    bool result = execute_control_transfer(target_device_address,cmd,data,max_packet_size);
    if (result)
        status = *data;
    free (data);
    return status;
}
bool set_packet_filter2 (uint8_t target_device_address,uint8_t interface_id,uint8_t packet_filter)
{
    uint8_t cmd[] = {0b00100001,0x43,packet_filter,0,interface_id,0,0,0}; // set ethernet packet filter
    uint8_t* data=(uint8_t*) malloc (max_packet_size);
    //bool result = execute_control_transfer(target_device_address,cmd,NULL,max_packet_size,0,data);
    bool result = execute_control_transfer(target_device_address,cmd,data,max_packet_size);
    free (data);
    return result;
}

///////////////////////////////////////////////////////////////////////////
// USB HUB commands
bool get_hub_descriptor2 (uint8_t target_device_address,uint8_t* buffer, int& buffer_length)
{
    //bmRequestType, bRequest, wValue, wIndex, wLength
    uint8_t cmd[] = {0b10100000,6,0,0x29,0,0,sizeof(USB_HUB_DESCRIPTOR),0};
    uint8_t* data=(uint8_t*) malloc (max_packet_size);
    //bool result = execute_control_transfer(target_device_address,cmd,NULL,max_packet_size,0,data);
    bool result = execute_control_transfer(target_device_address,cmd,data,max_packet_size);
    if (result)
    {
        print_buffer (data,*(data));
        memcpy(buffer, data, *(data));
        buffer_length+=*(data);
    }
    free(data);
    return result;
}
uint32_t get_hub_portstatus (uint8_t target_device_address,uint8_t portnr)
{
    //bmRequestType, bRequest, wValue, wIndex, wLength
    uint8_t cmd[] = {0b10100011,0,0,0,portnr,0,4,0};
    uint8_t* data=(uint8_t*) malloc (max_packet_size);
    //bool result = execute_control_transfer(target_device_address,cmd,NULL,max_packet_size,0,data);
    bool result = execute_control_transfer(target_device_address,cmd,data,max_packet_size);
    uint32_t retval = 0;
    if (result)
    {
        //print_buffer (data,4);
        memcpy (&retval,data,4);

        uint16_t portstatus = 0;
        memcpy (&portstatus,data,2);
        printf ("Port %d status: ",portnr);
        std::string status="";
        if (portstatus & 0b1)
            status += "connected,";
        if (portstatus & 0b10)
            status += "enabled,";
        if (portstatus & 0b100)
            status += "suspended,";
        if (portstatus & 0b1000)
            status += "reset,";
        if (portstatus & 0b100000000)
            status += "powered,";
        if (portstatus & 0b1000000000)
            status += "low-speed,";
        if (portstatus & 0b10000000000)
            status += "high-speed,";
        if (portstatus & 0b1000000000000)
            status += "indicator control";
        printf ("%s\n",status.c_str());

        uint16_t portchange = 0;
        memcpy (&portchange,data+2,2);
        printf ("Port %d change: ",portnr);
        status="";
        if (portchange & 0b1)
            status += "C_PORT_CONNECTION,";
        if (portchange & 0b10)
            status += "C_PORT_ENABLE,";
        if (portchange & 0b100)
            status += "C_PORT_SUSPEND,";
        if (portchange & 0b1000)
            status += "C_PORT_OVER_CURRENT,";
        if (portchange & 0b10000)
            status += "C_PORT_RESET,";
        printf ("%s\n",status.c_str());

    }
    free(data);
    return retval;
}
bool set_hub_port_feature2 (uint8_t target_device_address,uint8_t feature_selector,uint8_t port,uint8_t value)
{
    //bmRequestType, bRequest, wValue, wIndex, wLength
    uint8_t cmd[] = {0b00100011,0x03,feature_selector,0,port,value,0,0};
    uint8_t* data=(uint8_t*) malloc (max_packet_size);
    //bool result = execute_control_transfer(target_device_address,cmd,NULL,max_packet_size,0,data);
    bool result = execute_control_transfer(target_device_address,cmd,data,max_packet_size);
    free (data);
    return result;
}
bool clear_hub_port_feature2 (uint8_t target_device_address,uint8_t feature_selector,uint8_t port,uint8_t value)
{
    //bmRequestType, bRequest, wValue, wIndex, wLength
    uint8_t cmd[] = {0b00100011,0x01,feature_selector,0,port,value,0,0};
    uint8_t* data=(uint8_t*) malloc (max_packet_size);
    //bool result = execute_control_transfer(target_device_address,cmd,NULL,max_packet_size,0,data);
    bool result = execute_control_transfer(target_device_address,cmd,data,max_packet_size);
    free (data);
    return result;
}
///////////////////////////////////////////////////////////////////////////

///////////////////////////////////////////////////////////////////////////
// USB HID BOOT DEVICE INTERRUPT READOUT
bool read_boot_mouse (uint8_t target_device_address,uint8_t mouse_endpoint_id,uint8_t mouse_millis,uint16_t mouse_in_packetsize)
{
    uint8_t endpoint_toggle = 0;
    while (true)
    {
        uint8_t* buffer= (uint8_t* )malloc (mouse_in_packetsize);;
        uint8_t status = data_in_transfer(mouse_in_packetsize, target_device_address,mouse_endpoint_id, max_packet_size, endpoint_toggle,buffer);
        if (status != CH375_USB_INT_SUCCESS)
            return false;
        uint8_t buttonstate = buffer[0];
        uint8_t x = buffer[1];
        uint8_t y = buffer[2];
        printf ("left: %d, right: %d, middle: %d - X: %d, Y: %d\n",buttonstate&0x01,buttonstate&0x02,buttonstate&0x04,x,y);
        free (buffer);
        std::this_thread::sleep_for(std::chrono::milliseconds(mouse_millis));
        if (buttonstate&0x02) //right button
            return false;
    }
    return true;
}

void add_a_not_in_b_to_c (uint8_t (&c)[7],uint8_t (&a)[7],uint8_t (&b)[7])
{
  int idx=0;

  for (int i=0;i<sizeof (a);i++)
  {
    int j;
    for (j=0;j<sizeof(b);j++)
    {
      if (a[i]==b[j])
        break;
    }
    if (j==sizeof(b))
    {
      // a element not found in b, add to c
      c[idx++]=a[i];
    }
    else
    {
      // nothing to do
    }
  }
}
uint8_t old_key_buffer[7];
uint8_t key_downs[7];
uint8_t key_ups[7];
bool caps_lock = false;
bool num_lock = false;  
///////////////////////////////////////////////////////////////////////////////////
// converts a scancode into the appropriate bits L of the corresponding MSX key row
// we do the heavy lifting here so that the loop() function is simple and can react
// fast to the pulses on the keyboard connector
void write_msx_keyboard (uint8_t (&key_buffer)[7],uint8_t target_device_address,uint8_t interface_id)
{
  uint8_t ku_idx=0;
  uint8_t kd_idx=0;

  // make a list of key down's
  memset (key_downs,0,sizeof(key_downs));
  memset (key_ups,0,sizeof(key_ups));

  add_a_not_in_b_to_c (key_downs,key_buffer,old_key_buffer);
  add_a_not_in_b_to_c (key_ups,old_key_buffer,key_buffer);
  
  //print_buffer (key_buffer,sizeof(key_buffer));
  //print_buffer (key_downs,sizeof(key_downs));
  //print_buffer (key_ups,sizeof(key_ups));
  for (int i=0;i<sizeof(key_downs);i++)
  {
    if (key_downs[i]==0)
      break;
    //msx_key_matrix (key_downs[i],true);
    //Serial.print (" D:");
    //Serial.println (key_downs[i],HEX);
    printf ("D: %0X\n",key_downs[i]);

    if (key_downs[i]==0x39) // CAPS-LOCK
    {
        caps_lock = !caps_lock;
        uint8_t out_report = 0b00000000;
        if (caps_lock)
            out_report |= 0b00000010;
        else
            out_report &= 0b11111101;
        //data_out_transfer (&out_report,sizeof (out_report),1,1,max_packet_size,endpoint_out_toggle);
        set_report2 (target_device_address,2,0,interface_id,&out_report,sizeof(out_report));
    }
    if (key_downs[i]==0x53) // NUM-LOCK
    {
        num_lock = !num_lock;
        uint8_t out_report = 0b00000000;
        if (num_lock)
            out_report |= 0b00000001;
        else
            out_report &= 0b11111110;
        //data_out_transfer (&out_report,sizeof (out_report),1,1,max_packet_size,endpoint_out_toggle);
        set_report2 (target_device_address,2,0,interface_id,&out_report,sizeof(out_report));
    }
  }
  for (int i=0;i<sizeof(key_ups);i++)
  {
    if (key_ups[i]==0)
      break;
    //msx_key_matrix (key_ups[i],false);
    //Serial.print (" U:");
    //Serial.println (key_ups[i],HEX);
    printf ("U: %0X\n",key_ups[i]);
  }
  // use previous state to figure out key up/downs
  memcpy (old_key_buffer,key_buffer,sizeof (old_key_buffer));
}
uint8_t key_buffer[7];
bool read_boot_keyboard (uint8_t target_device_address,uint8_t interface_id, uint8_t endpoint_id,uint8_t millis,uint16_t in_packetsize)
{
    uint8_t endpoint_in_toggle = 0;
    while (true)
    {
        uint8_t* buffer = (uint8_t* )malloc (in_packetsize);
        uint8_t status = data_in_transfer(in_packetsize, target_device_address,endpoint_id, max_packet_size, endpoint_in_toggle,buffer);
        if (status != CH375_USB_INT_SUCCESS)
            return false;
        uint8_t modifier_keys = buffer[0];
        uint8_t reserved = buffer[1];
        uint8_t keycode1 = buffer[2];
        uint8_t keycode2 = buffer[3];
        uint8_t keycode3 = buffer[4];
        uint8_t keycode4 = buffer[5];
        uint8_t keycode5 = buffer[6];
        uint8_t keycode6 = buffer[7];
        //printf ("modifier_keys: %02X, keycode1:%02X, keycode2:%02X, keycode3:%02X, keycode4:%02X, keycode5:%02X, keycode6:%02X\n",modifier_keys,keycode1,keycode2,keycode3,keycode4,keycode5,keycode6);
        //////////////////////////////////////
        if (buffer[0])
            buffer[1] = buffer[0] | 0b10000000; // set high bit to 1
        else
            buffer[1] = 0;
        memcpy (key_buffer,buffer+1,sizeof(key_buffer));
        write_msx_keyboard (key_buffer,target_device_address,interface_id);
        //////////////////////////////////////
        free (buffer);
        //std::this_thread::sleep_for(std::chrono::milliseconds(millis));
        if (keycode1==0x14) // Q for quit
            return false;
    }
    return true;
}
///////////////////////////////////////////////////////////////////////////
// USB ETHERNET DEVICE INTERRUPT READOUT
bool check_network_connection (uint8_t target_device_address,uint8_t endpoint_id,uint8_t millis,uint16_t in_packetsize)
{
    uint8_t endpoint_toggle = 0;
    int count = 500;
    bool result = false;

    struct _ecm_notification_event
    {
        uint8_t bmRequestType;
        uint8_t bNotificationCode;
        uint16_t wValue;
        uint16_t wIndex;
        uint16_t wLength;
    } ecm_notification_event;
    while (--count > 0 && !result)
    {
        uint8_t* buffer = (uint8_t* )malloc (in_packetsize); 
        uint8_t status = data_in_transfer(in_packetsize, target_device_address,endpoint_id, max_packet_size, endpoint_toggle,buffer);
        if (status != CH375_USB_INT_SUCCESS)
            return false;
        memcpy (&ecm_notification_event,buffer,sizeof (_ecm_notification_event));
        //print_buffer (buffer,in_packetsize);
        if (ecm_notification_event.bmRequestType == 0b10100001) // device to host, class, endpoint communication
        {
            switch (ecm_notification_event.bNotificationCode)
            {
                case 0x00: // NETWORK_CONNECTION
                    //if (ecm_notification_event.wValue==0)
                    //    printf ("network cable DISCONNECTED on interface %d\n",*(buffer+4));
                    if (ecm_notification_event.wValue==1)
                        result = true;
                    //    printf ("network cable CONNECTED on interface %d\n",*(buffer+4));
                    break;
                case 0x01: // RESPONSE_AVAILABLE
                    //printf ("response available on interface %d\n",*(buffer+4));
                    break;
                case 0x2A: // CONNECTION_SPEED_CHANGE
                    //long speed_down = *(buffer+8) + *(buffer+9)*256+ *(buffer+10)*65536 + *(buffer+11)*4294967296;
                    //long speed_up = *(buffer+12) + *(buffer+13)*256+ *(buffer+14)*65536 + *(buffer+15)*4294967296;
                    //printf ("connection speed change on interface %d, %ld Mbps down / %ld Mbps up\n",*(buffer+4),speed_down/(8*1024*1024),speed_up/(8*1024*1024));
                    break;
            }
        }
        free (buffer);
        std::this_thread::sleep_for(std::chrono::milliseconds(millis));
    }
    return result;
}

void dump_in_packets (uint8_t target_device_address,uint8_t endpoint_id,uint16_t in_packetsize)
{
    uint8_t endpoint_toggle = 0;
    int count = 5;
    in_packetsize=1514;

    set_retry (0x0f);    
    while (count)
    {
        uint8_t* buffer = (uint8_t* )malloc (in_packetsize);
        //const clock_t begin_time = clock();
        uint8_t status = data_in_transfer(in_packetsize, target_device_address,endpoint_id, max_packet_size, endpoint_toggle,buffer);
        //std::cout << std::fixed << std::showpoint << float( clock () - begin_time ) /  CLOCKS_PER_SEC << std::endl;
        if (status != CH375_USB_INT_SUCCESS)
            continue;
        
        printf ("\n%d - dst: %02x:%02x:%02x:%02x:%02x:%02x - src: %02x:%02x:%02x:%02x:%02x:%02x - type: %04x",
            count,
            *(buffer+0),*(buffer+1),*(buffer+2),*(buffer+3),*(buffer+4),*(buffer+5), // dst
            *(buffer+6),*(buffer+7),*(buffer+8),*(buffer+9),*(buffer+10),*(buffer+11), // src
            ((*(buffer+12))<<8)+((*(buffer+13))));// EtherType

        print_buffer (buffer,in_packetsize);

        count --;
    }
    set_retry (0x8f);
}
///////////////////////////////////////////////////////////////////////////
// USB HUB DEVICE INTERRUPT READOUT
uint8_t get_hub_change (uint8_t target_device_address,uint8_t endpoint_id,uint8_t millis,uint16_t in_packetsize)
{
    uint8_t value = 0;
    uint8_t endpoint_toggle = 0;
    uint8_t* buffer = (uint8_t* ) malloc (in_packetsize);
    uint8_t status = data_in_transfer(in_packetsize, target_device_address,endpoint_id, max_packet_size, endpoint_toggle,buffer);
    if (status != CH375_USB_INT_SUCCESS)
        return 0;
    //print_buffer (buffer,in_packetsize);
    value = buffer[0];
    free (buffer);   
    std::this_thread::sleep_for(std::chrono::milliseconds(millis));
    return value;
}

bool get_descriptors (uint8_t address, uint8_t* buffer, int& buffer_length)
{
    uint8_t* buffer_ptr;

    bool result = get_device_descriptor2(0,buffer, buffer_length);
    if (!result && address==1) // only for first device try low speed
    {
        // 2-set to 1.5 Mhz low-speed mode, 0-set to 12 Mhz high-speed mode (default)
        set_speed(2);
        result = get_device_descriptor2(0,buffer, buffer_length);
    }
    if (!result)
        error("unable to get device descriptor");

    if (!set_address2 (address))
            error ("error setting address");

    for (int i=0;i<device.bNumConfigurations;i++)
    {
        buffer_ptr = buffer+buffer_length;
        result = get_configuration_descriptor2(address,i,buffer_ptr,buffer_length);
        if (!result)
            error("unable to get config descriptor");
    }
    return true;
}
void print_descriptors (uint8_t device_address, uint8_t* buffer, int buffer_length)
{ 
    USB_DEVICE_DESCRIPTOR* device;
    USB_CONFIG_DESCRIPTOR* config;
    USB_INTERF_DESCRIPTOR* interface;
    USB_ENDPOINT_DESCRIPTOR* endpoint;
    USB_HID_DESCRIPTOR* hid;
    USB_ETHERNET_HEADER_DESCRIPTOR* header;
    USB_ETHERNET_UNION_DESCRIPTOR* unione;
    USB_ETHERNET_DESCRIPTOR* ethernet;
    USB_HUB_DESCRIPTOR* hub;

    uint8_t *ptr = buffer;
    while (ptr<buffer+buffer_length)
    {
        std::string endpoint_type;
        std::string endpoint_address_type;
        std::string interface_class_name;
        std::string interface_protocol_name;
        std::string interface_subclass_name;
        std::string device_class_name;
        printf ("\n");
        switch (*(ptr+1))
        {
            case 0x01: // DEVICE_DESCRIPTOR
                device = (USB_DEVICE_DESCRIPTOR*) ptr;
                printf ("Device Descriptor:\n");
                printf ("  bLength\t\t\t%d\n",device->bLength);
                printf ("  bDescriptorType\t\t%d\n",device->bDescriptorType);
                printf ("  bcdUSB\t\t\t%d.%d\n",(device->bcdUSB & 0xff00)>>8, device->bcdUSB & 0xff);
                if (device->bDeviceClass==0xff)
                    device_class_name = "Vendor Specific Class";
                if (device->bDeviceClass==0x02)
                    device_class_name = "Communications";
                if (device->bDeviceClass==0x03)
                    device_class_name = "HID";
                if (device->bDeviceClass==0x09)
                    device_class_name = "Hub";
                if (device->bDeviceClass==0x0A)
                    device_class_name = "CDC Data";
                printf ("  bDeviceClass\t\t\t%d\t%s\n",device->bDeviceClass,device_class_name.c_str());
                printf ("  bDeviceSubClass\t\t%d\n",device->bDeviceSubClass);
                printf ("  bDeviceProtocol\t\t%d\n",device->bDeviceProtocol);
                printf ("  bMaxPacketSize0\t\t%d\n",device->bMaxPacketSize0);
                printf ("  idVendor\t\t\t0x%04x\n",device->idVendor);
                printf ("  idProduct\t\t\t0x%04x\n",device->idProduct);
                printf ("  bcdDevice\t\t\t%d.%d\n",(device->bcdDevice & 0xff00)>>8, device->bcdDevice & 0xff);
                printf ("  iManufacturer\t\t\t%d\n",device->iManufacturer);
                printf ("  iProduct\t\t\t%d\t%s\n",device->iProduct,get_string2 (device_address,device->iProduct).c_str());
                printf ("  iSerial\t\t\t%d\t%s\n",device->iSerial,get_string2 (device_address,device->iSerial).c_str());
                printf ("  bNumConfigurations\t\t%d\n",device->bNumConfigurations);
                ptr += *ptr;
                break;
            case 0x02: // CONFIG_DESCRIPTOR
                config = (USB_CONFIG_DESCRIPTOR*) ptr;
                printf ("  Configuration Descriptor:\n");
                printf ("    bLength\t\t\t%d\n",config->bLength);
                printf ("    bDescriptorType\t\t%d\n",config->bDescriptorType);
                printf ("    wTotalLength\t\t%d\n",config->wTotalLength);
                printf ("    bNumInterfaces\t\t%d\n",config->bNumInterfaces);
                printf ("    bConfigurationvalue\t\t%d\n",config->bConfigurationvalue);
                printf ("    iConfiguration\t\t%d\t%s\n",config->iConfiguration,get_string2 (device_address,config->iConfiguration).c_str());
                printf ("    bmAttributes\t\t%d\n",config->bmAttributes);
                printf ("    bMaxPower\t\t\t%d\n",config->bMaxPower);
                device->bNumConfigurations--;
                ptr += *ptr;
                break;
            case 0x04: // interface descriptor
                interface = (USB_INTERF_DESCRIPTOR*) ptr;
                printf ("    Interface Descriptor:\n");
                printf ("      bLength\t\t\t%d\n",interface->bLength);
                printf ("      bDescriptorType\t\t%d\n",interface->bDescriptorType);
                printf ("      bInterfaceNumber\t\t%d\n",interface->bInterfaceNumber);
                printf ("      bAlternateSetting\t\t%d\n",interface->bAlternateSetting);
                printf ("      bNumEndpoints\t\t%d\n",interface->bNumEndpoints);
                if (interface->bInterfaceClass==0xff)
                    interface_class_name = "Vendor Specific Class";
                if (interface->bInterfaceClass==0x02)
                    interface_class_name = "Communications";
                if (interface->bInterfaceClass==0x03)
                    interface_class_name = "HID";
                if (interface->bInterfaceClass==0x08)
                    interface_class_name = "Storage";
                if (interface->bInterfaceClass==0x09)
                    interface_class_name = "Hub";
                if (interface->bInterfaceClass==0x0A)
                    interface_class_name = "CDC Data";
                printf ("      bInterfaceClass\t\t%d\t%s\n",interface->bInterfaceClass,interface_class_name.c_str());
                if (interface->bInterfaceClass==0x03 && interface->bInterfaceSubClass==0x01)
                    interface_subclass_name = "Boot";
                if (interface->bInterfaceClass==0x02 && interface->bInterfaceSubClass==0x06)
                {
                    interface_subclass_name = "Ethernet Networking Control Model";
                    ethernet_info = new _ethernet_info();
                    ethernet_info->ethernet_control_interface = interface->bInterfaceNumber;
                }
                if (interface->bInterfaceClass==0x08 && interface->bInterfaceSubClass==0x06)
                    interface_subclass_name = "SCSI command set";
                if (interface->bInterfaceClass==0x0A && interface->bInterfaceSubClass==0x00)
                {
                    ethernet_info->ethernet_data_interface = interface->bInterfaceNumber;
                    if (interface->bAlternateSetting!=0)
                        ethernet_info->ethernet_alternate_setting = interface->bAlternateSetting;
                }
                printf ("      bInterfaceSubClass\t%d\t%s\n",interface->bInterfaceSubClass,interface_subclass_name.c_str());
                if (interface->bInterfaceClass==0x03 && interface->bInterfaceProtocol==0x01)
                {
                    interface_protocol_name = "Keyboard";
                    if (!hid_info) hid_info = new _hid_info();
                    hid_info->keyboard_interface = interface->bInterfaceNumber;
                }
                if (interface->bInterfaceClass==0x03 && interface->bInterfaceProtocol==0x02)
                {
                    interface_protocol_name = "Mouse";
                    if (!hid_info) hid_info = new _hid_info();
                    hid_info->mouse_interface = interface->bInterfaceNumber;
                }
                if (interface->bInterfaceClass==0x09 && interface->bInterfaceProtocol==0x00)
                {
                    interface_protocol_name = "No TT";
                    if (!hub_info) hub_info = new _hub_info();
                    hub_info->hub_interface = interface->bInterfaceNumber;
                }
                if (interface->bInterfaceClass==0x09 && interface->bInterfaceProtocol==0x01)
                {
                    interface_protocol_name = "Single TT";
                    if (!hub_info) hub_info = new _hub_info();
                    hub_info->hub_interface = interface->bInterfaceNumber;
                }
                if (interface->bInterfaceClass==0x09 && interface->bInterfaceProtocol==0x02)
                {
                    interface_protocol_name = "Multi TT";
                    if (!hub_info) hub_info = new _hub_info();
                    hub_info->hub_interface = interface->bInterfaceNumber;
                }
                if (interface->bInterfaceClass==0x08 && interface->bInterfaceSubClass==0x06 && interface->bInterfaceProtocol==0x50)
                {
                    interface_protocol_name = "BBB";
                    storage_info = new _storage_info();
                    storage_info->interface_id = interface->bInterfaceNumber;
                    storage_info->configuration_id = config->bConfigurationvalue;
                }
                printf ("      bInterfaceProtocol\t%d\t%s\n",interface->bInterfaceProtocol,interface_protocol_name.c_str());
                printf ("      iInterface\t\t%d\t%s\n",interface->iInterface,get_string2 (device_address,interface->iInterface).c_str());
                ptr += *ptr;
                break;
            case 0x05: // endpoint descriptor
                endpoint = (USB_ENDPOINT_DESCRIPTOR*) ptr;
                printf ("    Endpoint Descriptor:\n");
                printf ("      bLength\t\t\t%d\n",endpoint->bLength);
                printf ("      bDescriptorType\t\t%d\n",endpoint->bDescriptorType);
                endpoint_address_type = endpoint->bEndpointAddress&0b10000000 ? "IN" : "OUT";
                printf ("      bEndpointAddress\t\t%d\t%s\n",endpoint->bEndpointAddress&0b01111111,endpoint_address_type.c_str());
                if ((endpoint->bmAttributes&0b00000011) == 0b00)
                    endpoint_type = "Control";
                if ((endpoint->bmAttributes&0b00000011) == 0b01)
                    endpoint_type = "Isochronous";
                if ((endpoint->bmAttributes&0b00000011) == 0b10)
                    endpoint_type = "Bulk";
                if ((endpoint->bmAttributes&0b00000011) == 0b11)
                    endpoint_type = "Interrupt";
                printf ("      bmAttributes\t\t%d\t%s\n",endpoint->bmAttributes,endpoint_type.c_str());
                printf ("      wMaxPacketSize\t\t%d\n",endpoint->wMaxPacketSize);
                printf ("      bInterval\t\t\t%d\n",endpoint->bInterval);
                if (interface->bInterfaceClass==0x03 && interface->bInterfaceProtocol==0x01) // keyboard
                {
                    hid_info->keyboard_endpoint = endpoint->bEndpointAddress&0b01111111;
                    hid_info->keyboard_packetsize = endpoint->wMaxPacketSize;
                    hid_info->keyboard_millis = endpoint->bInterval;
                    hid_info->configuration_id = config->bConfigurationvalue;
                }
                if (interface->bInterfaceClass==0x03 && interface->bInterfaceProtocol==0x02) // mouse
                {
                    hid_info->mouse_endpoint = endpoint->bEndpointAddress&0b01111111;
                    hid_info->mouse_packetsize = endpoint->wMaxPacketSize;
                    hid_info->mouse_millis = endpoint->bInterval;
                    hid_info->configuration_id = config->bConfigurationvalue;
                }
                if (interface->bInterfaceClass==0x02 && interface->bInterfaceSubClass==0x06) // ethernet control
                {
                    if ((endpoint->bmAttributes&0b00000011) == 0b11) // interrupt
                    {
                        ethernet_info->ethernet_interrupt_endpoint = endpoint->bEndpointAddress&0b01111111;
                        ethernet_info->ethernet_interrupt_millis = endpoint->bInterval;
                        ethernet_info->ethernet_interrupt_packetsize = endpoint->wMaxPacketSize;
                    }
                    ethernet_info->configuration_id = config->bConfigurationvalue;
                }
                if (interface->bInterfaceClass==0x0a && interface->bInterfaceSubClass==0x00) // ethernet data
                {
                    if ((endpoint->bmAttributes&0b00000011) == 0b10 && endpoint->bEndpointAddress&0b10000000) // bulk IN
                    {
                        ethernet_info->ethernet_bulk_in_endpoint = endpoint->bEndpointAddress&0b01111111;
                        ethernet_info->ethernet_bulk_in_packetsize = endpoint->wMaxPacketSize;
                    }      
                    if ((endpoint->bmAttributes&0b00000011) == 0b10 && !(endpoint->bEndpointAddress&0b10000000)) // bulk OUT
                    {
                        ethernet_info->ethernet_bulk_out_endpoint = endpoint->bEndpointAddress&0b01111111;
                        ethernet_info->ethernet_bulk_out_packetsize = endpoint->wMaxPacketSize;
                    }                     
                }
                if (interface->bInterfaceClass==0x09 && (endpoint->bmAttributes&0b00000011) == 0b11) // interrupt
                {
                    hub_info->hub_interrupt_endpoint = endpoint->bEndpointAddress&0b01111111;
                    hub_info->hub_interrupt_packetsize = endpoint->wMaxPacketSize;
                    hub_info->hub_interrupt_millis = endpoint->bInterval;
                    hub_info->configuration_id = config->bConfigurationvalue;
                }
                if (interface->bInterfaceClass==0x08 && interface->bInterfaceSubClass==0x06 && interface->bInterfaceProtocol==0x50)
                {
                    if ((endpoint->bmAttributes&0b00000011) == 0b10 && endpoint->bEndpointAddress&0b10000000) // bulk IN
                    {
                        storage_info->bulk_in_endpoint_id = endpoint->bEndpointAddress&0b01111111;
                        storage_info->bulk_in_packetsize = endpoint->wMaxPacketSize;
                    }      
                    if ((endpoint->bmAttributes&0b00000011) == 0b10 && !(endpoint->bEndpointAddress&0b10000000)) // bulk OUT
                    {
                        storage_info->bulk_out_endpoint_id = endpoint->bEndpointAddress&0b01111111;
                        storage_info->bulk_out_packetsize = endpoint->wMaxPacketSize;
                    }                     
                }
                ptr += *ptr;
                break;
            case 0x21: // HID descriptor
                hid = (USB_HID_DESCRIPTOR*) ptr;
                printf ("      HID Descriptor:\n");
                printf ("        bLength\t\t\t%d\n",hid->bLength);
                printf ("        bDescriptorType\t\t%d\n",hid->bDescriptorType);
                printf ("        bcdHID\t\t\t%d.%d\n",(hid->hid_version & 0xff00)>>8, hid->hid_version & 0xff);
                printf ("        bCountryCode\t\t%d\n",hid->country_code);
                printf ("        bNumDescriptors\t\t%d\n",hid->num_descriptors);
                printf ("        bDescriptorType\t\t%d\n",hid->descriptor_type);
                printf ("        wDescriptorLength\t%d\n",hid->descriptor_length);
                ptr += *ptr;
                break;
            case 0x24: // CDC ECM / CS_INTERFACE
                printf ("    CDC ECM ");
                switch (*(ptr+2)) // subtype
                {
                    case 0x00: // header
                        printf ("header\n");
                        header = (USB_ETHERNET_HEADER_DESCRIPTOR*) ptr;
                        printf ("      bcdCDC\t\t\t%d.%d\n",(header->bcdCDC & 0xff00)>>8, header->bcdCDC & 0xff);
                        break;
                    case 0x06: // union
                        printf ("union\n");
                        unione = (USB_ETHERNET_UNION_DESCRIPTOR*) ptr;
                        printf ("      bControlInterface\t\t%d\n",unione->bControlInterface);
                        printf ("      bSubordinateInterface0\t%d\n",unione->bSubordinateInterface0);
                        break;
                    case 0x0f: // ethernet
                        printf ("ethernet\n");
                        ethernet = (USB_ETHERNET_DESCRIPTOR*) ptr;
                        printf ("      MAC\t\t\t%s\n",get_string2(device_address, ethernet->iMACAddress).c_str());
                        printf ("      wMaxSegmentSize\t\t%d\n",ethernet->wMaxSegmentSize);
                        break;
                    default:
                        printf ("unknown %02x\n",*(ptr+2));
                }
                ptr += *(ptr);
                break;
            case 0x29: // HUB
                hub = (USB_HUB_DESCRIPTOR*) ptr;
                printf ("  Hub Descriptor:\n");
                printf ("    bLength\t\t\t%d\n",hub->bLength);
                printf ("    bDescriptorType\t\t%x\n",hub->bDescriptorType);
                printf ("    bNrPorts\t\t\t%d\n",hub->bNrPorts);
                printf ("    wHubCharacteristics\t\t%x\n",hub->wHubCharacteristics);
                printf ("    bPwrOn2PwrGood\t\t%d\n",hub->bPwrOn2PwrGood);
                printf ("    bHubContrCurrent\t\t%d\n",hub->bHubContrCurrent);
                ptr += *(ptr);
                break;
            default:
                printf ("Unknown type: %02x\n",*(ptr+1));
                ptr += *ptr;
                break;
        }
    }
}
void do_hid (_hid_info&);
void do_ethernet (_ethernet_info&);
void do_hub (_hub_info&);
void do_storage (_storage_info&);

bool connect_disk ()
{
    writeCommand (CH376_CMD_DISK_CONNECT);
    if (waitStatus ()!=CH375_USB_INT_SUCCESS)
        return false;
    return true;
}
bool mount_disk ()
{
    int status;
    writeCommand (CH376_CMD_DISK_MOUNT);
    status = waitStatus ();
    if ((status==CH375_USB_INT_SUCCESS))
        return true;
    return false;
}
void abort_nak ()
{
    writeCommand (CH375_CMD_ABORT_NAK);
}
void open_file (const char* name)
{
    int status;
    writeCommand (CH376_CMD_SET_FILE_NAME);
    writeDataMultiple ((uint8_t*) name,strlen(name));
    writeData (0);
    writeCommand (CH376_CMD_OPEN_FILE);
    if ((status=waitStatus ())!=CH375_USB_INT_SUCCESS)
        error ("file not opened");
}
void open_dir (char* name)
{
    int status;
    writeCommand (CH376_CMD_SET_FILE_NAME);
    writeDataMultiple ((uint8_t*) name,strlen(name));
    writeData (0);
    writeCommand (CH376_CMD_OPEN_FILE);
    if ((status=waitStatus ())!=CH375_USB_ERR_OPEN_DIR)
        error ("directory not opened");
}

/* File directory information in FAT data area */
typedef struct _FAT_DIR_INFO {
uint8_t DIR_Name [11];; /* 00H, file name, a total of 11 bytes, fill in the blanks */
uint8_t DIR_Attr;; /* 0BH, file attributes, refer to the following instructions */
uint8_t DIR_NTRes;; /* 0CH */
uint8_t DIR_CrtTimeTenth;; /* 0DH, the time of file creation, counted in units of 0.1 seconds */
uint16_t DIR_CrtTime;; /* 0EH, file creation time */
uint16_t DIR_CrtDate;; /* 10H, date of file creation */
uint16_t DIR_LstAccDate;; /* 12H, the date of the last access operation */
uint16_t DIR_FstClusHI;; /* 14H */
uint16_t DIR_WrtTime;; /* 16H, file modification time, refer to the previous macro MAKE_FILE_TIME */
uint16_t DIR_WrtDate;; /* 18H, file modification date, refer to the previous macro MAKE_FILE_DATE */
uint16_t DIR_FstClusLO;; /* 1AH */
uint32_t DIR_FileSize;; /* 1CH, file length */
;} FAT_DIR_INFO;

void get_dirinfo (char* wildcard, std::vector<std::string>& contents)
{
    uint8_t status,value;
    char* pDot;
    char wild[8];
    strcpy (wild, wildcard);

    if ((pDot = strstr(wild,".")))
    {
        *pDot = '\0';
        pDot++;
    }

    // start query
    writeCommand (CH376_CMD_SET_FILE_NAME);
    writeDataMultiple ((uint8_t*) wildcard,strlen(wildcard));
    writeData (0);
    // open first file
    writeCommand (CH376_CMD_OPEN_FILE);
    if ((status=waitStatus ())!=CH375_USB_INT_DISK_READ)
        error ("file not opened");
    do 
    {
        // get file info
        writeCommand(CH375_CMD_RD_USB_DATA);
        ssize_t bytes = readData(&value);
        FAT_DIR_INFO* dirinfo = (FAT_DIR_INFO*) malloc (sizeof (FAT_DIR_INFO));
        readDataMultiple ((uint8_t*) dirinfo,value);
        // get file name
        if (dirinfo->DIR_Attr==0x20 || dirinfo->DIR_Attr==0x00)
        {
            if (strncmp ((char*) dirinfo->DIR_Name+8,pDot,3)==0)
            {
                std::string str;
                for (int i=0;i<11;i++)
                    str.append (1,(char) dirinfo->DIR_Name[i]);
                contents.push_back (str);
            }
        }
        free (dirinfo);
        // continue enumerating
        writeCommand (CH376_CMD_FILE_ENUM_GO);
        status=waitStatus ();
    } while (status==CH375_USB_INT_DISK_READ);

}

void read_file ()
{
    int status,count=2;
    while (count-- > 0)
    {
        writeCommand (CH376_CMD_BYTE_READ);
        writeData (128);
        writeData (0);
        status=waitStatus ();
        if (status==CH375_USB_INT_SUCCESS)
            return; // done
        if (status==CH375_USB_INT_DISK_READ)
        {
            uint8_t buffer[128];
            ssize_t len = read_usb_data(buffer,128);
            print_buffer (buffer,len);
            char line[65];
            strncpy (line,(char*) buffer,len);
            printf ("%s\n",line);
            writeCommand (CH376_CMD_BYTE_RD_GO);
            if ((status=waitStatus ())!=CH375_USB_INT_SUCCESS)
                error ("read file error");
        }
    }
}
void close_file ()
{
    int status;
    writeCommand (CH376_CMD_FILE_CLOSE);
    writeData (0);
    if ((status=waitStatus ())!=CH375_USB_INT_SUCCESS)
        error ("file not closed");
}

void usb_host_bus_reset ()
{
    uint8_t version;
    writeCommand (CH376_CMD_GET_IC_VER);
    readData (&version);
    if (version&0b00100000 == 0)
        error ("Not a right version\n");
    version = version&0b00011111;
    printf ("CH376 IC version: %d\n",version);

    bool result;
    result=set_usb_host_mode(CH375_USB_MODE_HOST);
    usleep (250000);
    result = set_usb_host_mode(CH375_USB_MODE_HOST_RESET);
    usleep (500000);
    if (!(result=set_usb_host_mode(CH375_USB_MODE_HOST)))
        error ("host mode not succeeded\n");
    usleep (250000);

    // configure the number of retries (indefinite)
    set_retry (0x8f);


}

std::vector <_hid_info> hids;
std::vector <_hub_info> hubs;
std::vector <_storage_info> storages;
std::vector <_ethernet_info> ethernets;

void init_device (uint8_t device_address)
{
    uint8_t buffer[1024];
    int buffer_length;
    hid_info=NULL;
    hub_info=NULL;
    ethernet_info=NULL;

    memset (buffer, 0, 1024);
    bool result = get_descriptors (device_address,buffer, buffer_length);
    if (!result)
        error("unable to get descriptors");

    print_descriptors (device_address, buffer, buffer_length);
    
    if (hid_info)
    {
        hid_info->device_address = device_address;
        if (!set_configuration2(hid_info->device_address,hid_info->configuration_id))
                error ("error setting Hid configuration");
        hids.push_back (*hid_info);
        hid_info=NULL;
    }
    if (ethernet_info)
    {
        ethernet_info->device_address = device_address;
        if (!set_configuration2(ethernet_info->device_address,ethernet_info->configuration_id))
                error ("error setting Ethernet configuration");
        ethernets.push_back (*ethernet_info);
        ethernet_info=NULL;
    }
    if (hub_info)
    {
        hub_info->device_address = device_address;
        if (!set_configuration2(hub_info->device_address,hub_info->configuration_id))
            error ("error setting Hub configuration");
        hubs.push_back (*hub_info);
        do_hub (*hub_info);
        hub_info=NULL;
    }
    if (storage_info)
    {
        storage_info->device_address = device_address;
        if (!set_configuration2(storage_info->device_address,storage_info->configuration_id))
                error ("error setting Storage configuration");
        storages.push_back (*storage_info);
        storage_info=NULL;
    }
}
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
