S0urceror/MSX-USB/test/usb_via_arduino/src/ch375_COM.c

#include < stdio.h >
#include < string.h >
#include < intrins.h >
#include " types.h "
#include " reg80390.h "
#include "ch375_inc.h"       // CH375 header file
#include "descriptor_COM.h" // Descriptor
#include " delay.h "
#include " main.h "

// #define USB_DEBUG

#ifdef USB_DEBUG
#include " uart.h "
#endif

mREQUEST_PACKET request;
mUART_PARA uartpara;

bit CH375FLAGERR;           // error flag
bit CH375CONFLAG;           //Is the device configured flag
bit ENDP2_NEED_UP_FLAG = 0; // Endpoint 2 has data to upload flag
bit ENDP2_UP_SUC_FLAG = 1;  // Endpoint 2 this time data upload success flag
bit SET_LINE_CODING_Flag;   // Class request SET_LINE_CODING flag

U8_T VarUsbAddress;    // Device address
U8_T mVarSetupRequest; // USB request code
U16_T mVarSetupLength; // Length of subsequent data
U8_T *VarSetupDescr;   // Descriptor offset address

/* Hardware related definitions */
volatile U8_T far CH375_CMD_PORT _at_ 0x180001; // I/O address of CH375 command port
volatile U8_T far CH375_DAT_PORT _at_ 0x180000; // I/O address of CH375 data port
sbit CH375_INT_WIRE = P2 ^ 7;                   // P2.7, INT0, connected to the INT# pin of CH375, used to query the interrupt status, REV20
// sbit CH375_INT_WIRE = P2^4; // REV23

#define USB_TIMEOUT 5

U8_T far DownBuf[300];
U8_T far UpBuf[300];
U8_T far USB_timeout = USB_TIMEOUT;
U16_T far DownCtr = 0;
U16_T far UpCtr = 0;
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
